hexaedron/home_bme280/src/getPressureTrend.cpp

#include <ch32v003fun.h>

#define PRESSURE_DELTA      64UL  // ~0.25 mmHg
#define PRESSURE_FULL_DELTA 256UL // 1 mmHg

int8_t getPressureTrend(uint32_t* pressureHistory, uint8_t pressureHistoryHours, uint32_t currentPressure)
{
    uint8_t i;
    uint32_t min = UINT32_MAX, max = 0;

    for(i = 0; i < pressureHistoryHours; i++)
    {
        if(max < pressureHistory[i])
            max = pressureHistory[i];

        if((min > pressureHistory[i]) && (pressureHistory[i] != 0))
            min = pressureHistory[i];
    }

    if(currentPressure > (max + PRESSURE_DELTA))
        return 1;

    if( (currentPressure > min) && ((currentPressure - min) > PRESSURE_FULL_DELTA) )
        return 1;

    if(currentPressure < (min - PRESSURE_DELTA))
        return -1;

    if( (currentPressure < max) && ((max - currentPressure) > PRESSURE_FULL_DELTA) )
        return -1;

    return 0;
}
