hexaedron/home_bme280/include/pack_settings.h

#ifndef _PACK_SETTINGS_H_
#define _PACK_SETTINGS_H_

#include <stdint.h>

uint8_t getBrigtness(void);

uint16_t getScreenChangeSeconds_x5(void);

void packSettings(uint8_t brigtnness, uint16_t screenChangeSeconds_x5, uint8_t& data0, uint8_t& data1);

#endif
