hexaedron/home_bme280/include/funconfig.h

#ifndef _FUNCONFIG_H
#define _FUNCONFIG_H

#define CH32V003                 1
#define FUNCONF_USE_PLL          0
#define FUNCONF_HSE_BYPASS       0
#define FUNCONF_USE_HSI          1
#define FUNCONF_SYSTICK_USE_HCLK 1

#endif
